drfailov/BatteryProtectorBoard/Software/Battery Protector Software (release)/charge_indicator 2018-08-13 01-30/TimerLed.ino

int timer_led_pin = 18;
long timerLEDblinkPeriod = 5000; //ms
long timerLEDblinkOffDuration = 50; //ms
long timerLEDblinkOnDuration = 300; //ms
int  timerLEDblinkTimes = 3; //сколько раз надо мигнуть
boolean timerLEDcurrentLedState = true;
int timerLEDcurrentBlink = 0; //0 ... 3 number of blink for current loop
long timerLEDlastActionTime = 0; //time when led changed state last time

//Задача в целом: мигать быстро по 3 раза с паузами в 5 секунд.
//Примерно так:
//#####################################--####--####--#####################################--####--####--#####################################--####--####--

void initTimerLed(){
  pinMode(timer_led_pin, OUTPUT); 
}

void timerLedLoop(){
  long timeAgo = millis() - timerLEDlastActionTime;
  if(timerLEDcurrentBlink > timerLEDblinkTimes && timeAgo > timerLEDblinkPeriod)
    timerLEDcurrentBlink = 0;
  if(timerLEDcurrentBlink <= timerLEDblinkTimes){
    if(timerLEDcurrentLedState == true && timeAgo > timerLEDblinkOnDuration){ //надо выключить
      timerLEDlastActionTime = millis();
      timerLEDcurrentLedState = false;
      digitalWrite(timer_led_pin, LOW);
      Serial.println("Timer led OFF");
    }
    else if(timerLEDcurrentLedState == false && timeAgo > timerLEDblinkOffDuration){ //надо включить
      timerLEDlastActionTime = millis();
      timerLEDcurrentLedState = true;
      digitalWrite(timer_led_pin, HIGH);
      Serial.println("Timer led ON");
      timerLEDcurrentBlink ++;
    }
  }
}
