drfailov/BatteryProtectorBoard/Software/Battery Protector Software (release)/charge_indicator 2018-08-10 20-36/ModeDischarged.ino

void modeDischargedSetup(){
  mosfetDisable();
  led(MAGENTA,BLACK,     MAGENTA,BLACK,     MAGENTA,BLACK,     MAGENTA,BLACK);
}

void modeDischargedLoop(){
  buttonLoop();
  ledLoop();
  mosfetLoop();
  voltageLoop();
}


void modeDischargedButtonDown(){
  
}


void modeDischargedButtonUp(){
  
}
