drfailov/BatteryProtectorBoard/Software/Battery Protector Software (release)/charge_indicator 2018-08-10 20-36/ModeOvervoltage.ino

void modeOvervoltageSetup(){
  mosfetDisable();
  led(GREEN,BLACK,     GREEN,BLACK,     GREEN,BLACK,     GREEN,BLACK);
}

void modeOvervoltageLoop(){
  buttonLoop();
  ledLoop();
  mosfetLoop();
  voltageLoop();
}


void modeOvervoltageButtonDown(){
  
}


void modeOvervoltageButtonUp(){
  
}
