drfailov/BatteryProtectorBoard/Software/Battery Protector Software (release)/charge_indicator 2018-08-10 20-36/Timer.ino

int timer_led_pin = 18;
long timerStartTime = -1; //-1 = disabled
long timerTime = -1; //-1 = disabled


void initTimer(){
  pinMode(timer_led_pin, OUTPUT);
  timerStartTime = -1;
  timerTime = -1;  
}

void timerLoop(){
  if(timerStartTime == -1)
    return;
  long passed = millis() - timerStartTime;
  long remaining = timerTime - passed;
  if(remaining <= 0){
    timerStartTime = -1;
    timerTime = -1;  
    Serial.println("Timer is out.");
    digitalWrite(timer_led_pin, LOW);
    setDisabledMode();
  }
}


void setTimer(long timeMs){  //-1 = off
  if(timeMs == -1){
    timerStartTime = -1;
    timerTime = -1;  
    Serial.println("Timer disabled.");
    digitalWrite(timer_led_pin, LOW);
    setNormalMode();
    return;
  }
  
  timerStartTime = millis();
  timerTime = timeMs;
  digitalWrite(timer_led_pin, HIGH);
  Serial.print("Timer set for ");
  if(timeMs < 1000L*60L){
    Serial.print(timeMs / 1000L);
    Serial.println(" sec.");
  }
  else if(timeMs < 1000L*60L*60L){
    Serial.print(timeMs / 60000L);
    Serial.println(" min.");
  }
  setNormalMode();
}
