drfailov/BatteryProtectorBoard/Software/Battery Protector Software (release)/charge_indicator 2018-08-10 20-36/ModeCalibrationHigh.ino

void modeCalibrationHighSetup(){
  led(BLUE,BLUE,     BLUE,BLUE,     BLUE,BLUE,     BLUE,GREEN);
}

void modeCalibrationHighLoop(){
  buttonLoop();
  ledLoop();
  mosfetLoop();
  voltageLoop();
}


void modeCalibrationHighButtonDown(){
  ledWaitFor(5, CYAN);
  calibrateMaximumVoltage();
  setCalibrationLowMode();
}


void modeCalibrationHighButtonUp(){
  
}
