drfailov/BatteryProtectorBoard/Software/Battery Protector Software (release)/charge_indicator 2018-08-10 20-36/ModeCalibrationLow.ino

void modeCalibrationLowSetup(){
  led(BLUE,RED,     BLUE,BLUE,     BLUE,BLUE,     BLUE,BLUE);
}

void modeCalibrationLowLoop(){
  buttonLoop();
  ledLoop();
  mosfetLoop();
  voltageLoop();
}


void modeCalibrationLowButtonDown(){
  ledWaitFor(5, MAGENTA);
  calibrateMinimumVoltage();
  setNormalMode();
  
}


void modeCalibrationLowButtonUp(){
  
}
